tadakado/ch552-dongle/src/breathe_lut.h

/* SPDX-License-Identifier: MIT */
/*
 * 呼吸パターン輝度テーブル（tools/gen_lut.py が生成。手で編集しないこと）
 *   位相 64 分割、知覚上の明るさを cos 半波で振り、ガンマ 2.2 を掛けて
 *   実際の WS2812 デューティに変換したもの。最大値は NEO_MAX(0x40)。
 *   人間の目には、暗い側で長く留まり明るい側で滑らかに折り返す。
 */
#ifndef BREATHE_LUT_H
#define BREATHE_LUT_H

#define BREATHE_STEPS 64

static __code const unsigned char breathe_lut[BREATHE_STEPS] = {
    0x00, 0x00, 0x00, 0x00, 0x00, 0x00, 0x00, 0x01,
    0x01, 0x02, 0x02, 0x03, 0x05, 0x07, 0x09, 0x0B,
    0x0E, 0x11, 0x15, 0x18, 0x1C, 0x21, 0x25, 0x29,
    0x2D, 0x31, 0x35, 0x38, 0x3B, 0x3D, 0x3F, 0x40,
    0x40, 0x40, 0x3F, 0x3D, 0x3B, 0x38, 0x35, 0x31,
    0x2D, 0x29, 0x25, 0x21, 0x1C, 0x18, 0x15, 0x11,
    0x0E, 0x0B, 0x09, 0x07, 0x05, 0x03, 0x02, 0x02,
    0x01, 0x01, 0x00, 0x00, 0x00, 0x00, 0x00, 0x00,
};

#endif /* BREATHE_LUT_H */
